FabLabUTFSM/WoodPulp-Filter---COVID-19/images/l1_0.jpg

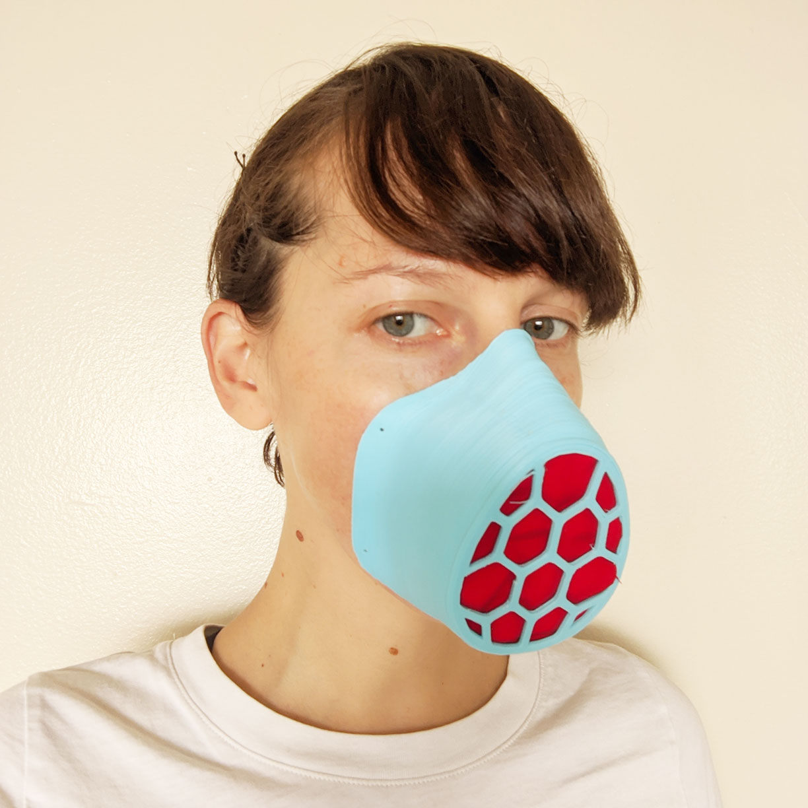
images/l1_0.jpg
