FabLabUTFSM/WoodPulp-Filter---COVID-19/SEM/SEM_CBA/BKP/SEM/AraucoBKP_1_20nmAu_top_0004_raw.jpg

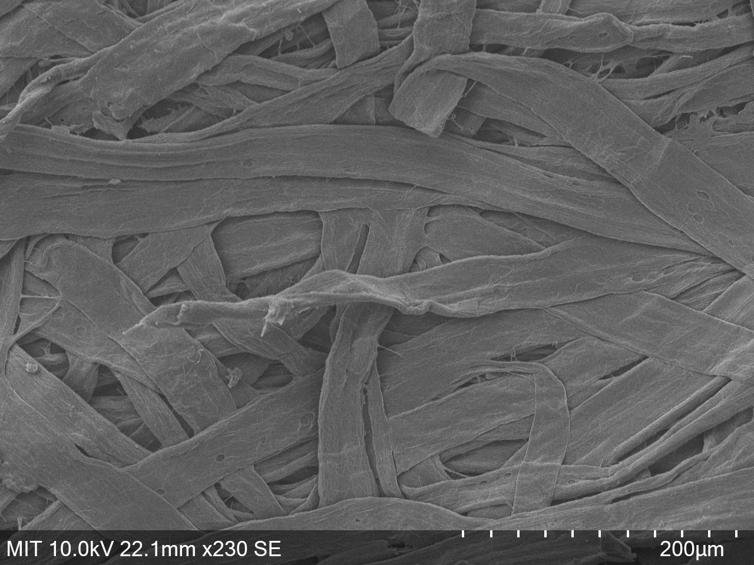
SEM/SEM_CBA/BKP/SEM/AraucoBKP_1_20nmAu_top_0004_raw.jpg
