FabLabUTFSM/WoodPulp-Filter---COVID-19/SEM/SEM_CBA/BKP/SEM/AraucoBKP_6_20nmAu_top_0002_raw.jpg

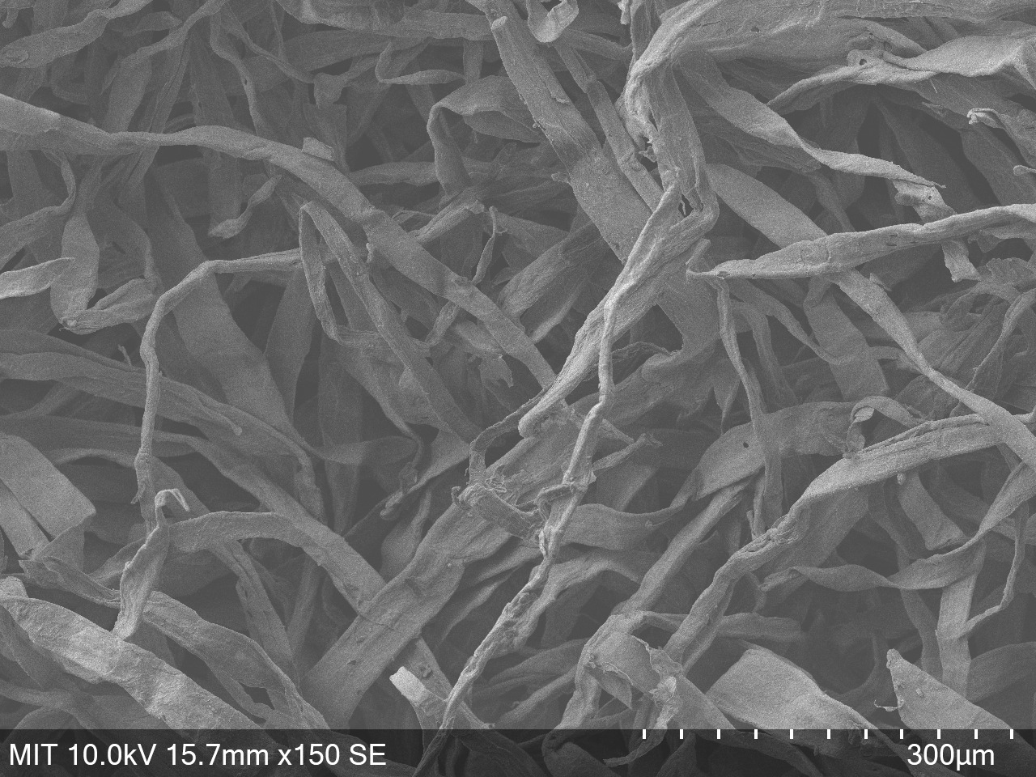
SEM/SEM_CBA/BKP/SEM/AraucoBKP_6_20nmAu_top_0002_raw.jpg
