FabLabUTFSM/WoodPulp-Filter---COVID-19/SEM/SEM_CBA/BKP/SEM/AraucoBKP_7_20nmAu_side_0002.jpg

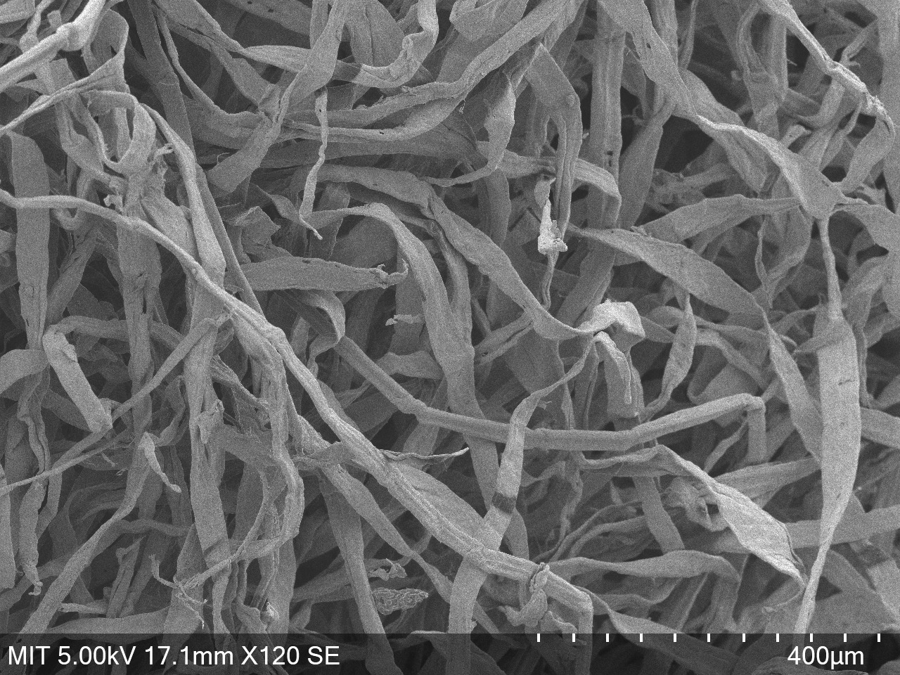
SEM/SEM_CBA/BKP/SEM/AraucoBKP_7_20nmAu_side_0002.jpg
