FabLabUTFSM/WoodPulp-Filter---COVID-19/SEM/SEM_CBA/EKP/SEM/AraucoEKP_1_20nmAu_top_0010.jpg

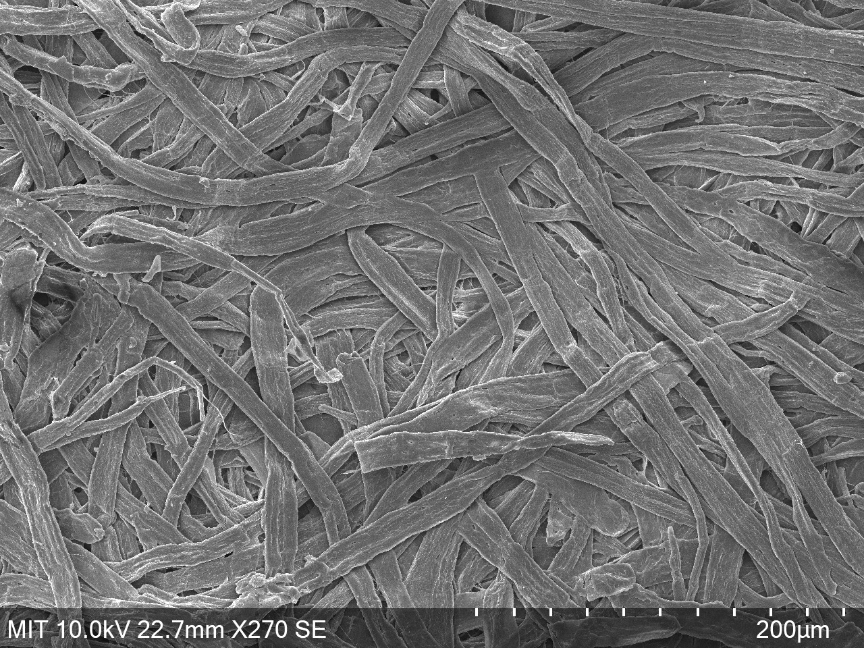
SEM/SEM_CBA/EKP/SEM/AraucoEKP_1_20nmAu_top_0010.jpg
