FabLabUTFSM/WoodPulp-Filter---COVID-19/SEM/SEM_CBA/EKP/SEM/AraucoEKP_8_20nmAu_top_0006.jpg

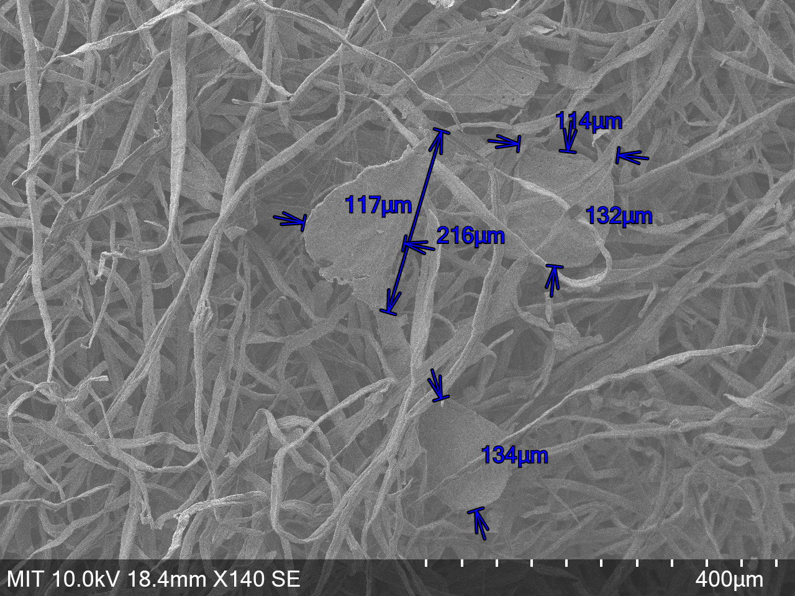
SEM/SEM_CBA/EKP/SEM/AraucoEKP_8_20nmAu_top_0006.jpg
