FabLabUTFSM/WoodPulp-Filter---COVID-19/SEM/SEM_CBA/UKP/SEM/AraucoUKP_1_20nmAu_top_0004.jpg

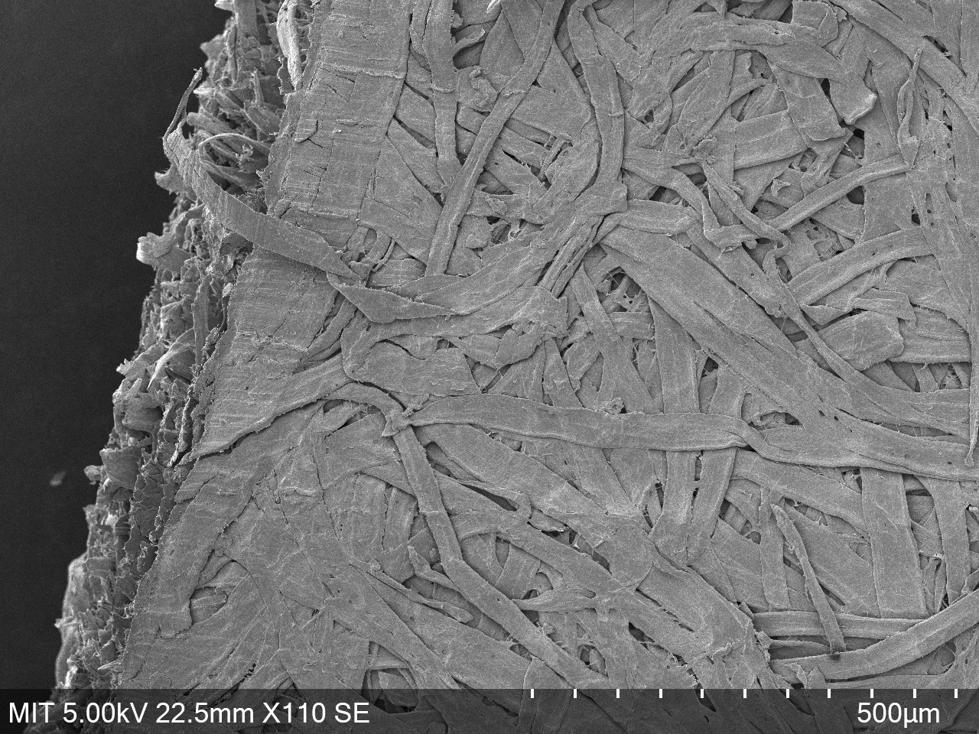
SEM/SEM_CBA/UKP/SEM/AraucoUKP_1_20nmAu_top_0004.jpg
