FabLabUTFSM/WoodPulp-Filter---COVID-19/SEM/SEM_CBA/UKP/SEM/AraucoUKP_6_20nmAu_top_0002.jpg

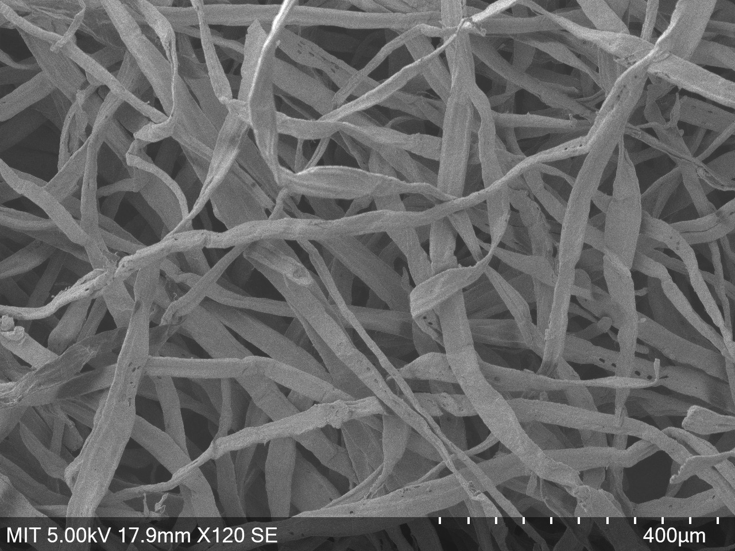
SEM/SEM_CBA/UKP/SEM/AraucoUKP_6_20nmAu_top_0002.jpg
