FabLabUTFSM/WoodPulp-Filter---COVID-19/SEM/SEM_UTFSM/BKP dwn _02.tif

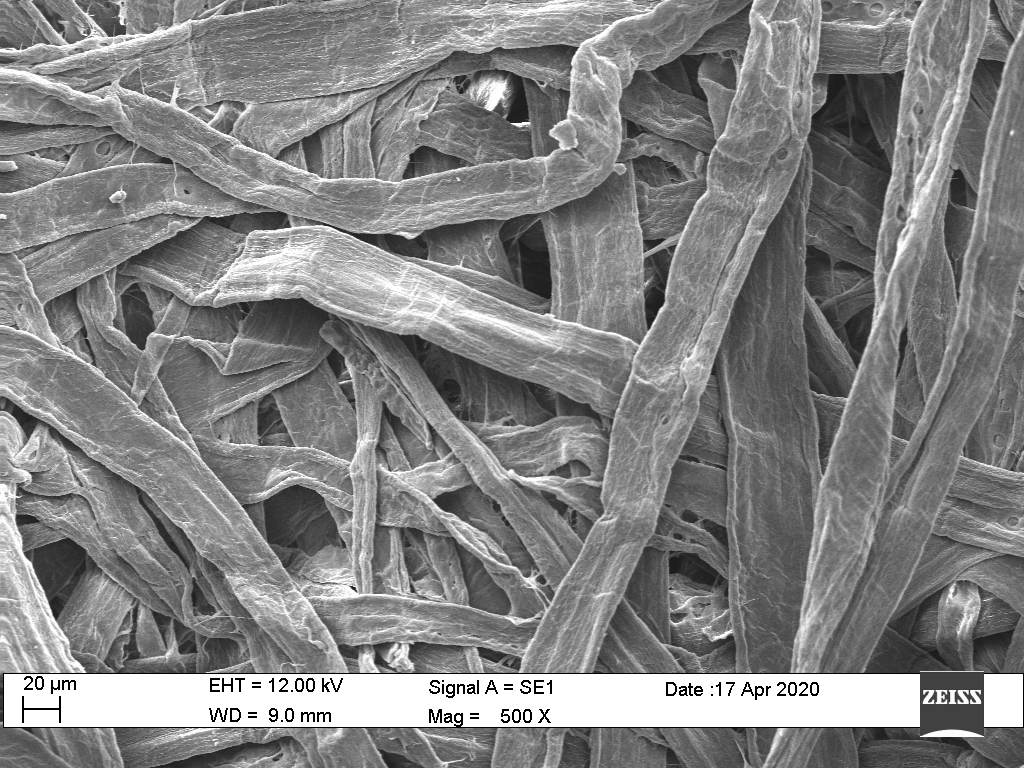
SEM/SEM_UTFSM/BKP dwn _02.tif
