FabLabUTFSM/WoodPulp-Filter---COVID-19/SEM/SEM_UTFSM/BKP up _01.tif

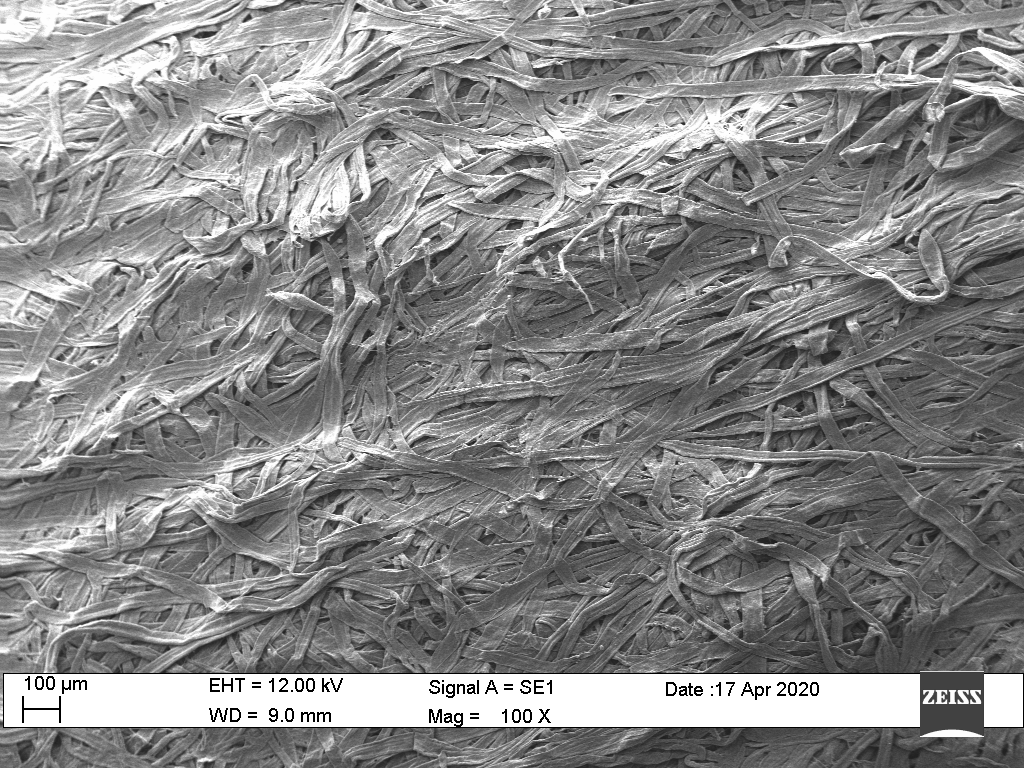
SEM/SEM_UTFSM/BKP up _01.tif
