FabLabUTFSM/WoodPulp-Filter---COVID-19/SEM/SEM_UTFSM/BKP up _03.tif

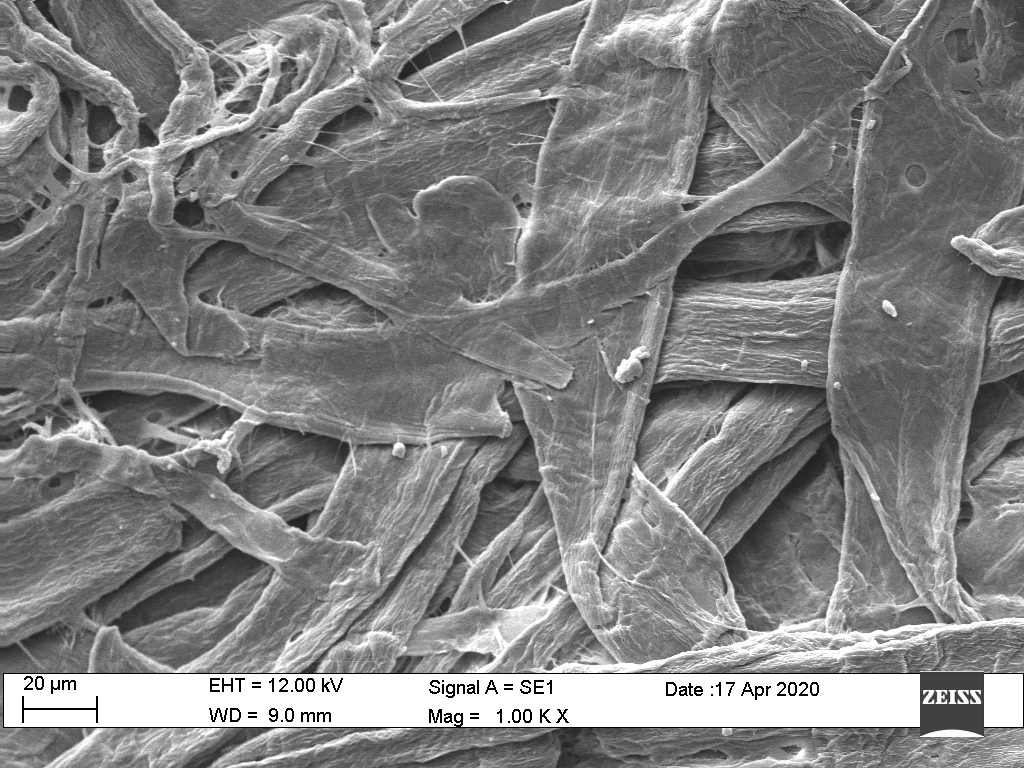
SEM/SEM_UTFSM/BKP up _03.tif
