FabLabUTFSM/WoodPulp-Filter---COVID-19/SEM/SEM_UTFSM/BKP up _04.tif

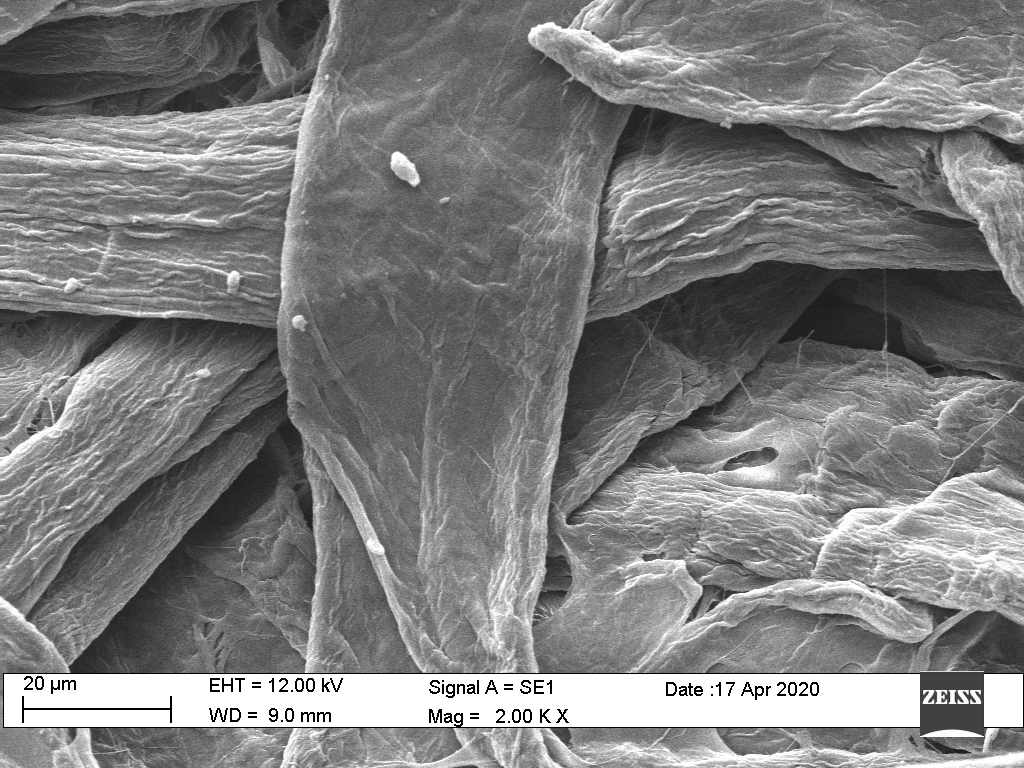
SEM/SEM_UTFSM/BKP up _04.tif
