FabLabUTFSM/WoodPulp-Filter---COVID-19/SEM/SEM_UTFSM/EKP dwn_01.tif

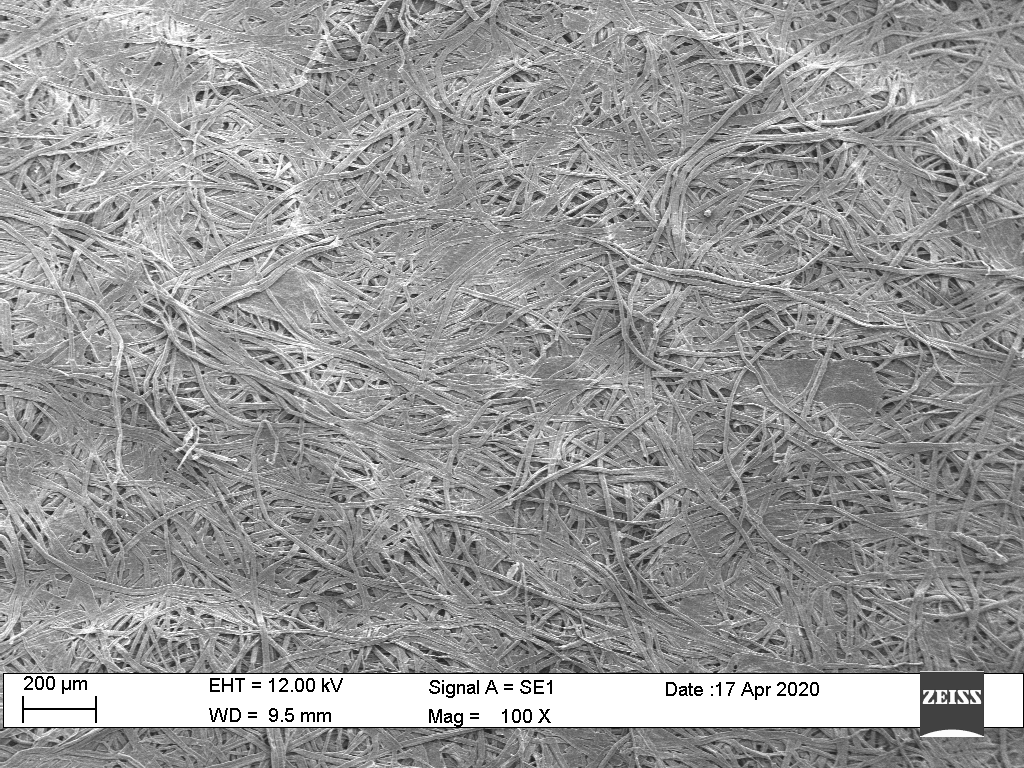
SEM/SEM_UTFSM/EKP dwn_01.tif
