FabLabUTFSM/WoodPulp-Filter---COVID-19/SEM/SEM_UTFSM/EKP dwn_03.tif

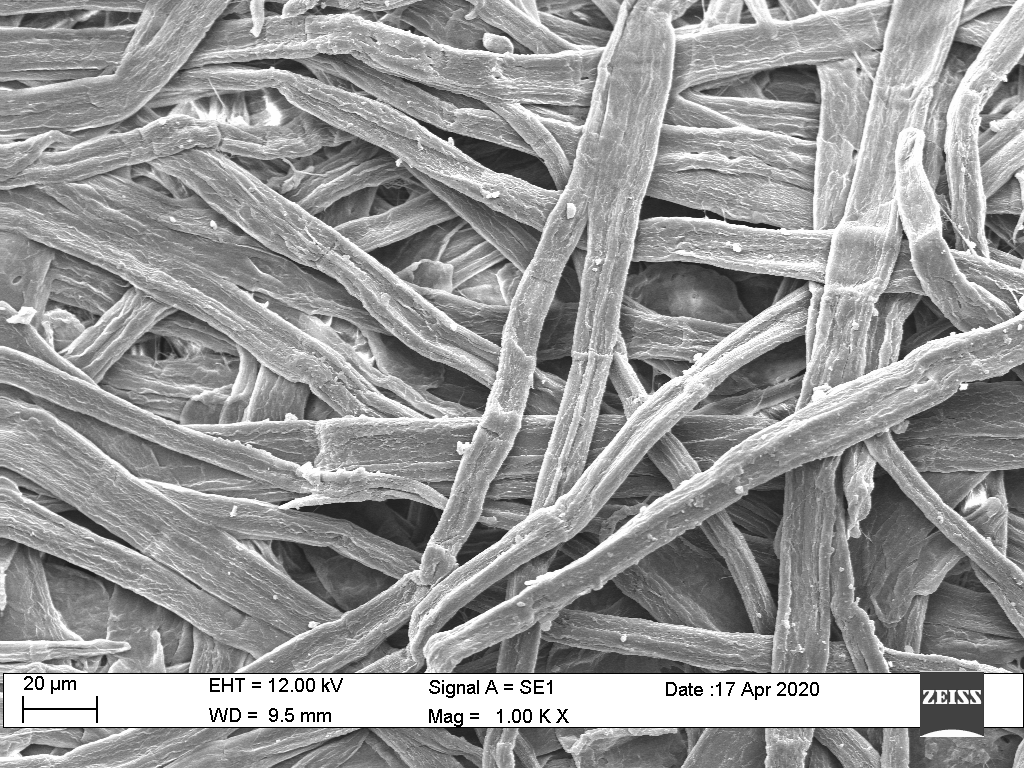
SEM/SEM_UTFSM/EKP dwn_03.tif
