FabLabUTFSM/WoodPulp-Filter---COVID-19/SEM/SEM_UTFSM/EKP up_01.tif

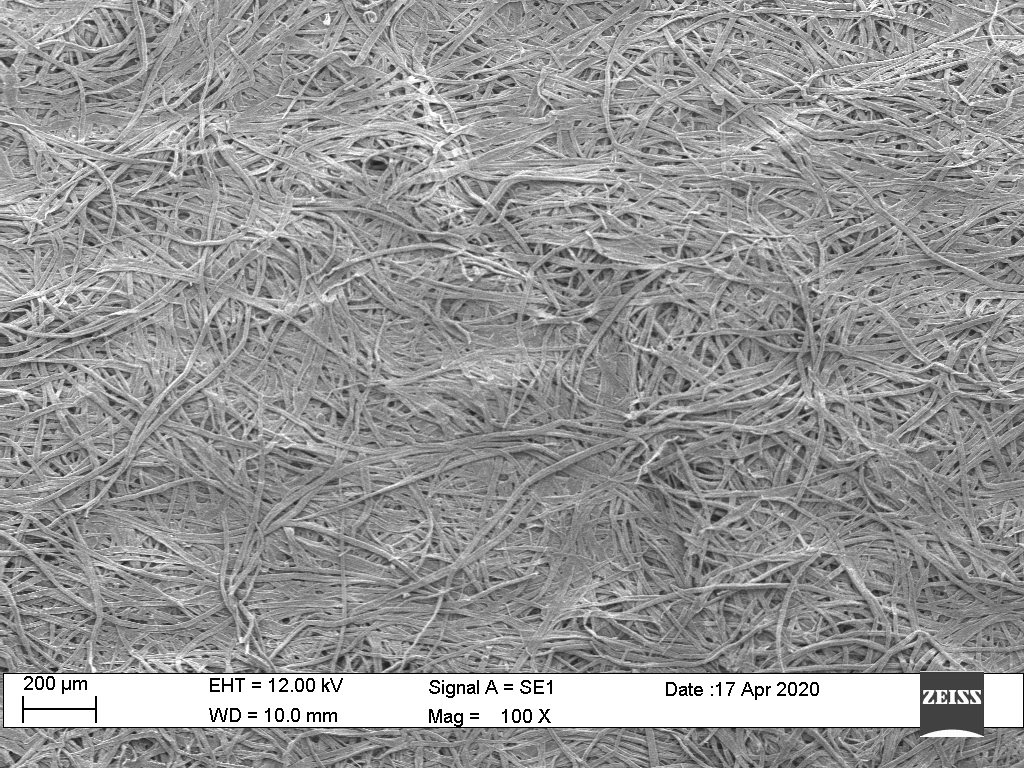
SEM/SEM_UTFSM/EKP up_01.tif
