FabLabUTFSM/WoodPulp-Filter---COVID-19/SEM/SEM_UTFSM/EKP up_02.tif

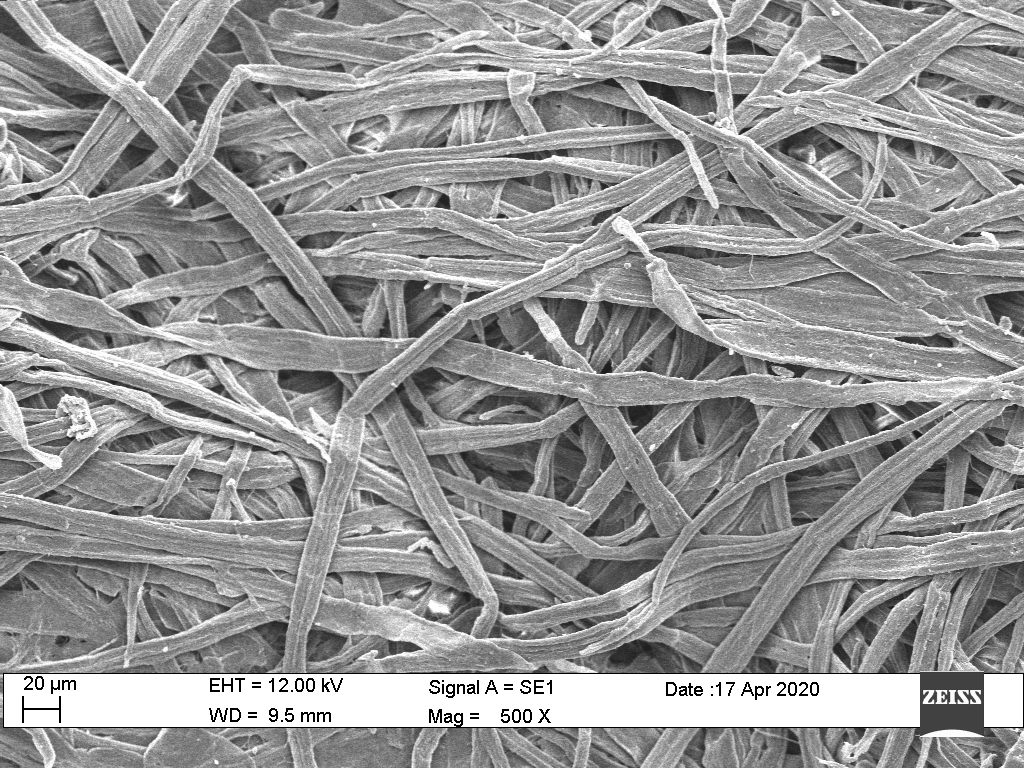
SEM/SEM_UTFSM/EKP up_02.tif
