FabLabUTFSM/WoodPulp-Filter---COVID-19/SEM/SEM_UTFSM/EKP up_04.tif

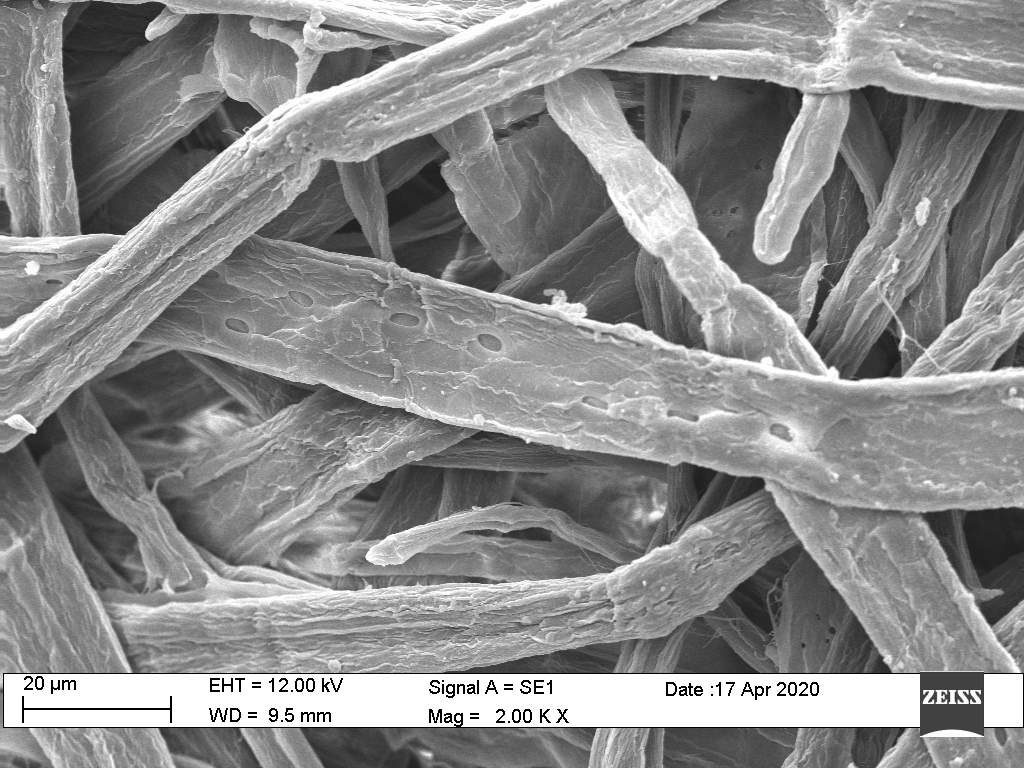
SEM/SEM_UTFSM/EKP up_04.tif
