FabLabUTFSM/WoodPulp-Filter---COVID-19/SEM/SEM_UTFSM/UKP dwn_01.tif

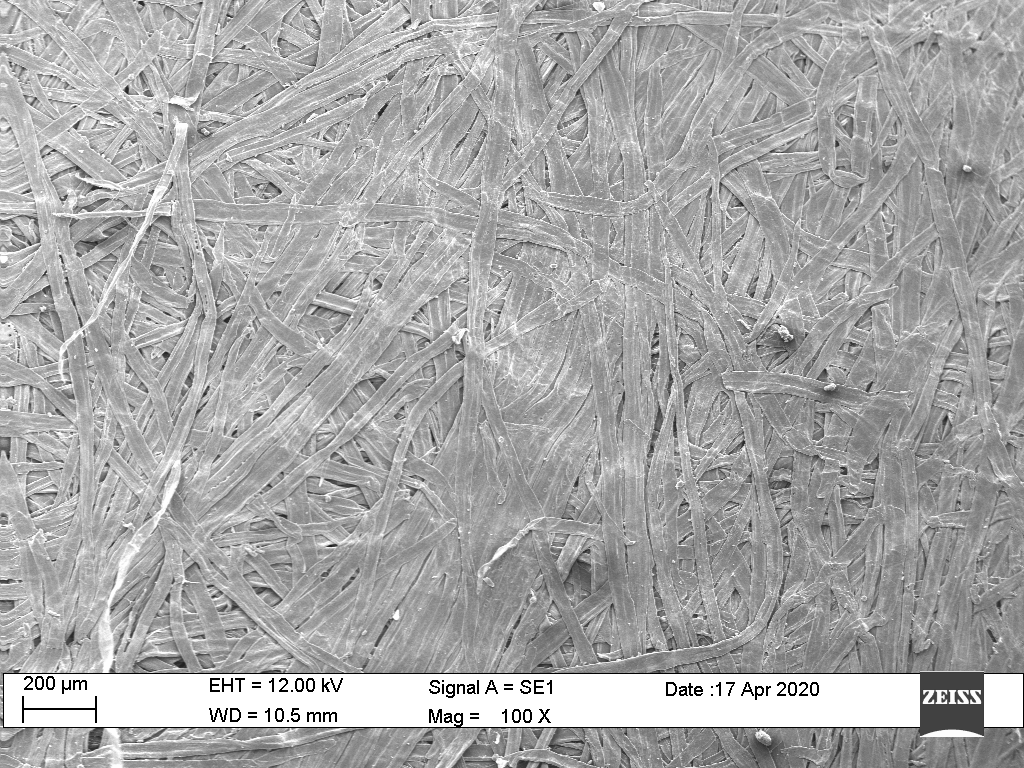
SEM/SEM_UTFSM/UKP dwn_01.tif
