FabLabUTFSM/WoodPulp-Filter---COVID-19/SEM/SEM_UTFSM/UKP dwn_03.tif

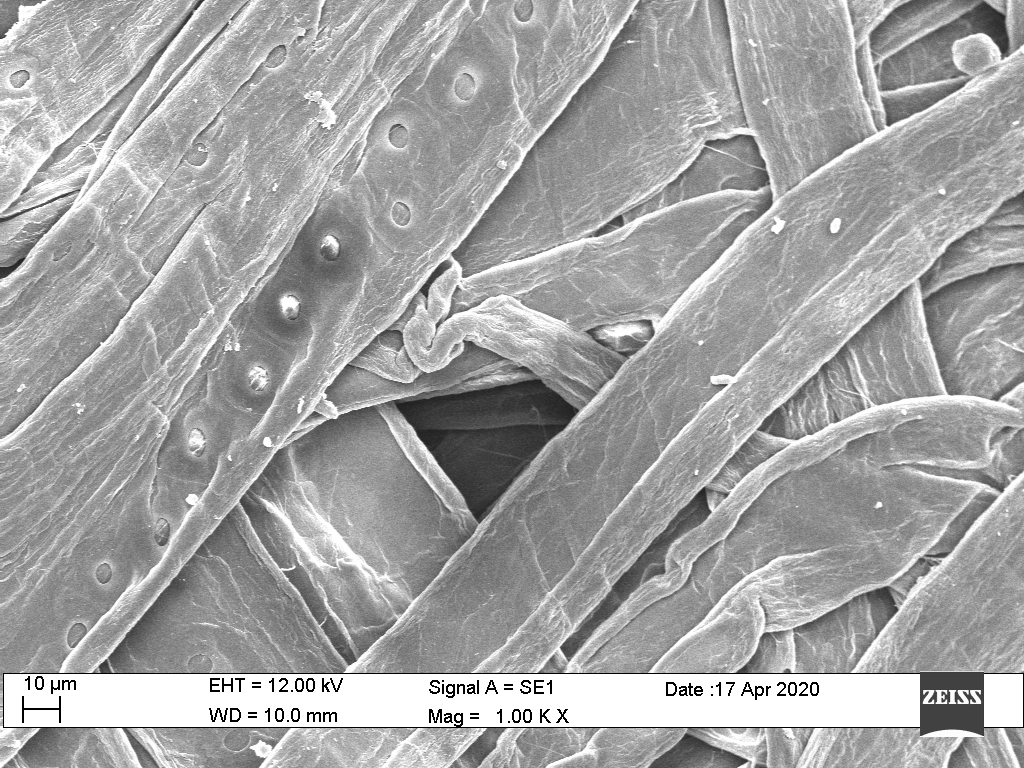
SEM/SEM_UTFSM/UKP dwn_03.tif
