FabLabUTFSM/WoodPulp-Filter---COVID-19/SEM/SEM_UTFSM/UKP up_01.tif

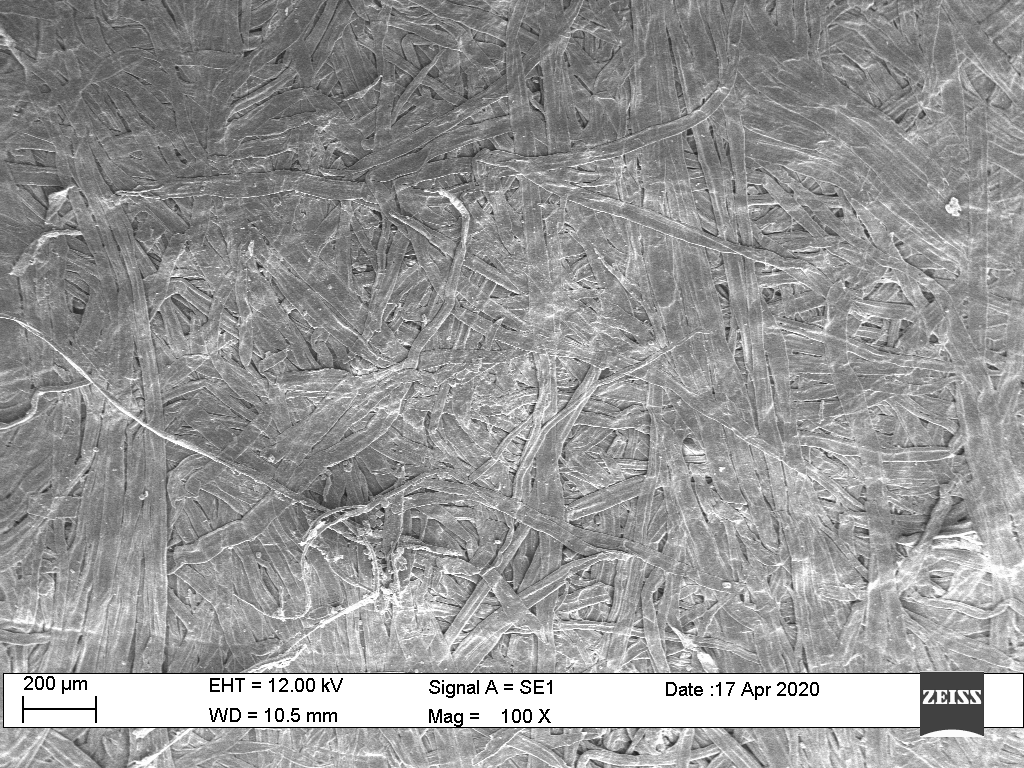
SEM/SEM_UTFSM/UKP up_01.tif
