FabLabUTFSM/WoodPulp-Filter---COVID-19/SEM/SEM_UTFSM/UKP up_03.tif

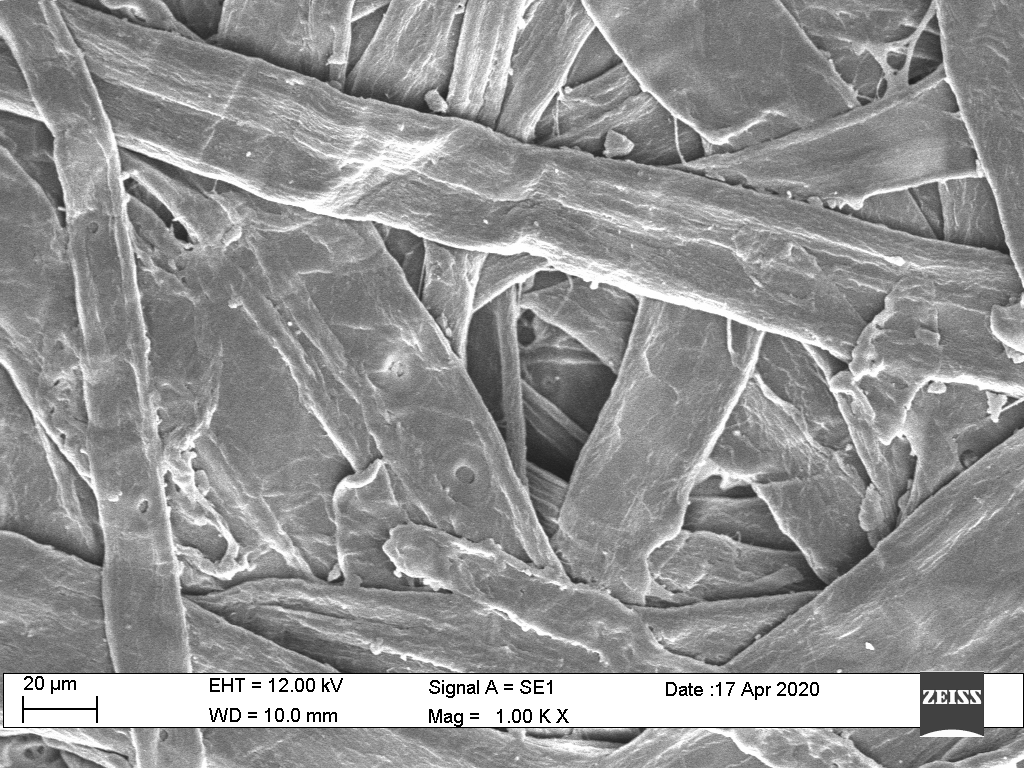
SEM/SEM_UTFSM/UKP up_03.tif
