FabLabUTFSM/WoodPulp-Filter---COVID-19/SEM/SEM_UTFSM/UKP up_04.tif

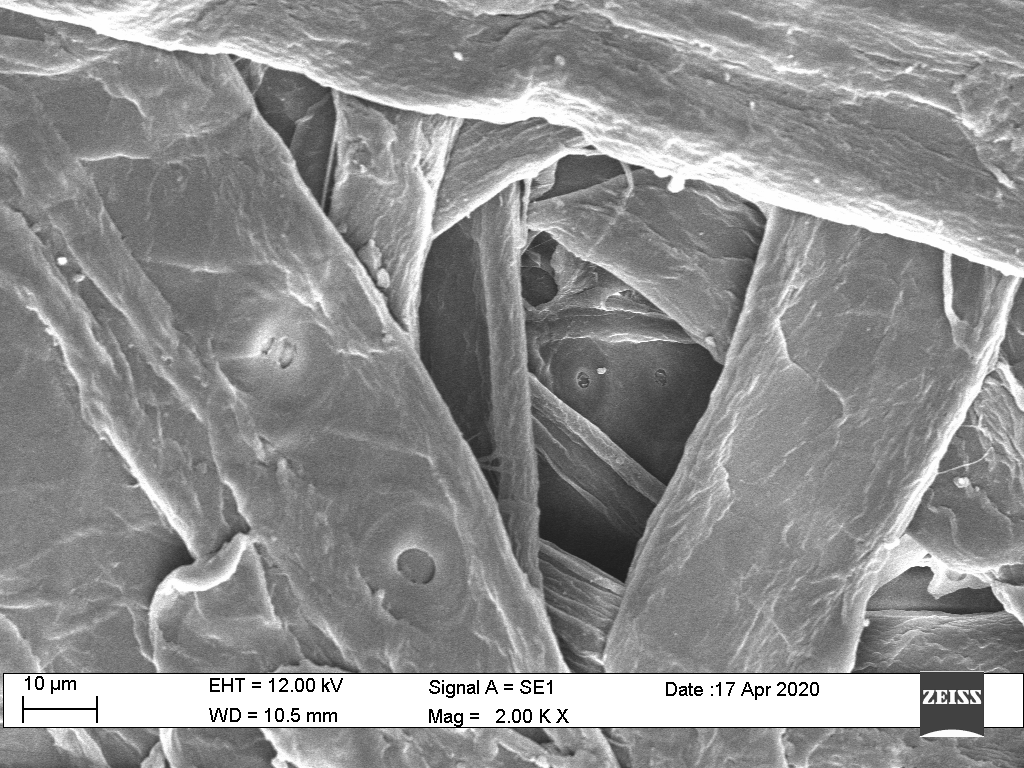
SEM/SEM_UTFSM/UKP up_04.tif
